celikada/IOTB/SW/IOTBKES/IOTBesp/src/secrets.h

// Use this file to store all of the private credentials 
// and connection details

#define SECRET_SSID "celikada"                                // replace MySSID with your WiFi network name
#define SECRET_PASS "Alya19Bt"                            // replace MyPassword with your WiFi password

#define SECRET_CH_ID 121256                                 // replace 0000000 with your channel number
#define SECRET_WRITE_APIKEY "BK5WQCU9Z57Y97VW"                           // replace XYZ with your channel write API Key

/*
Field 1 ambiance_temp
Field 2 ambiance_hum
Field 3 soil_temp
Field 4 soil_hum
Field 5 iotb_temp
Field 6 pump_relay
Field 7 water_level
*/
